eaome/watertanksensor/IMG_5381.jpeg

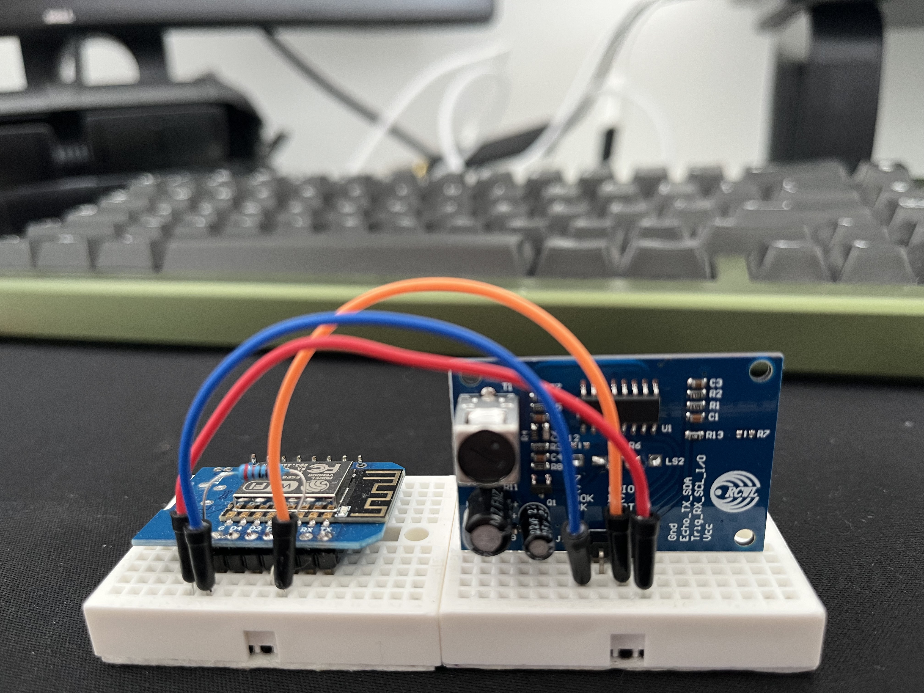
IMG_5381.jpeg
