eaome/watertanksensor/IMG_5385.jpeg

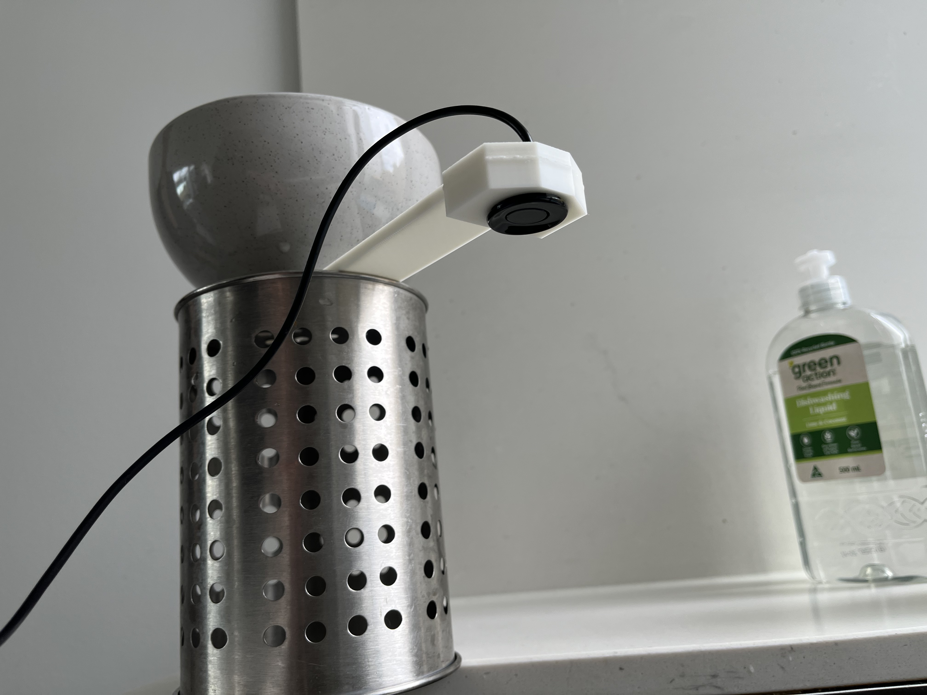
IMG_5385.jpeg
