eaome/watertanksensor/IMG_5386 2.PNG

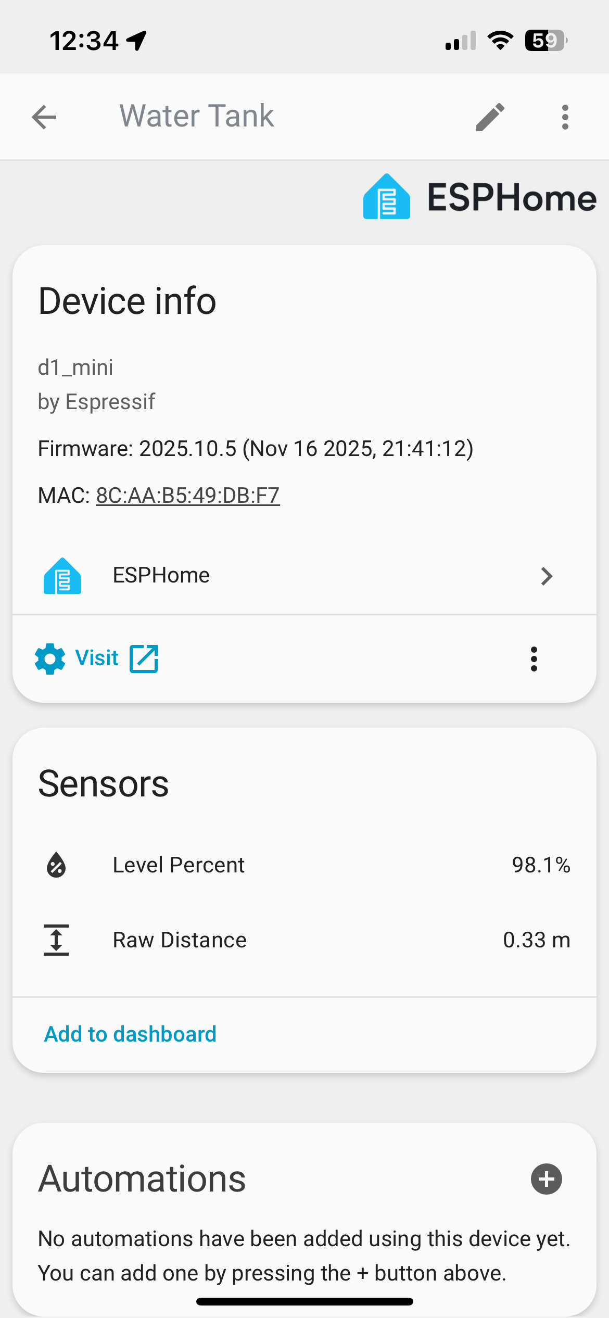
IMG_5386 2.PNG
