eaome/watertanksensor/IMG_5388.jpeg

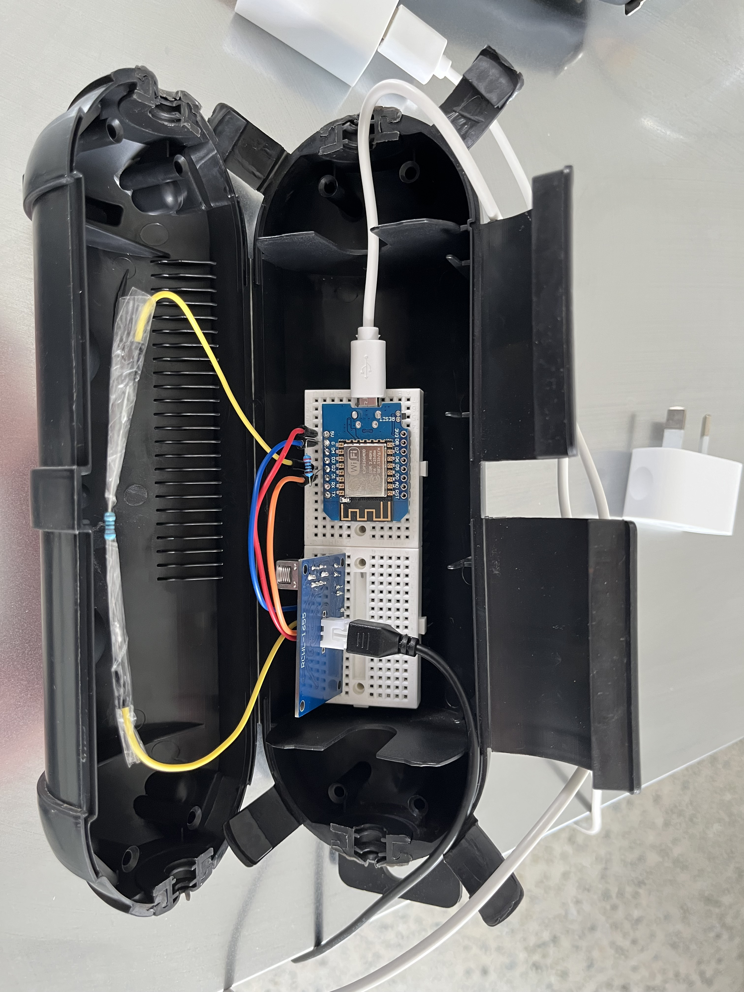
IMG_5388.jpeg
