eaome/watertanksensor/IMG_5384.jpeg

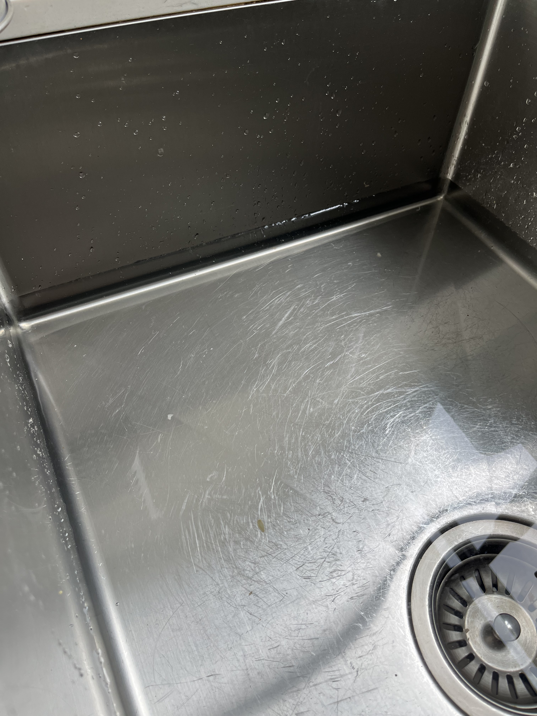
IMG_5384.jpeg
