eaome/watertanksensor/IMG_5390.jpeg

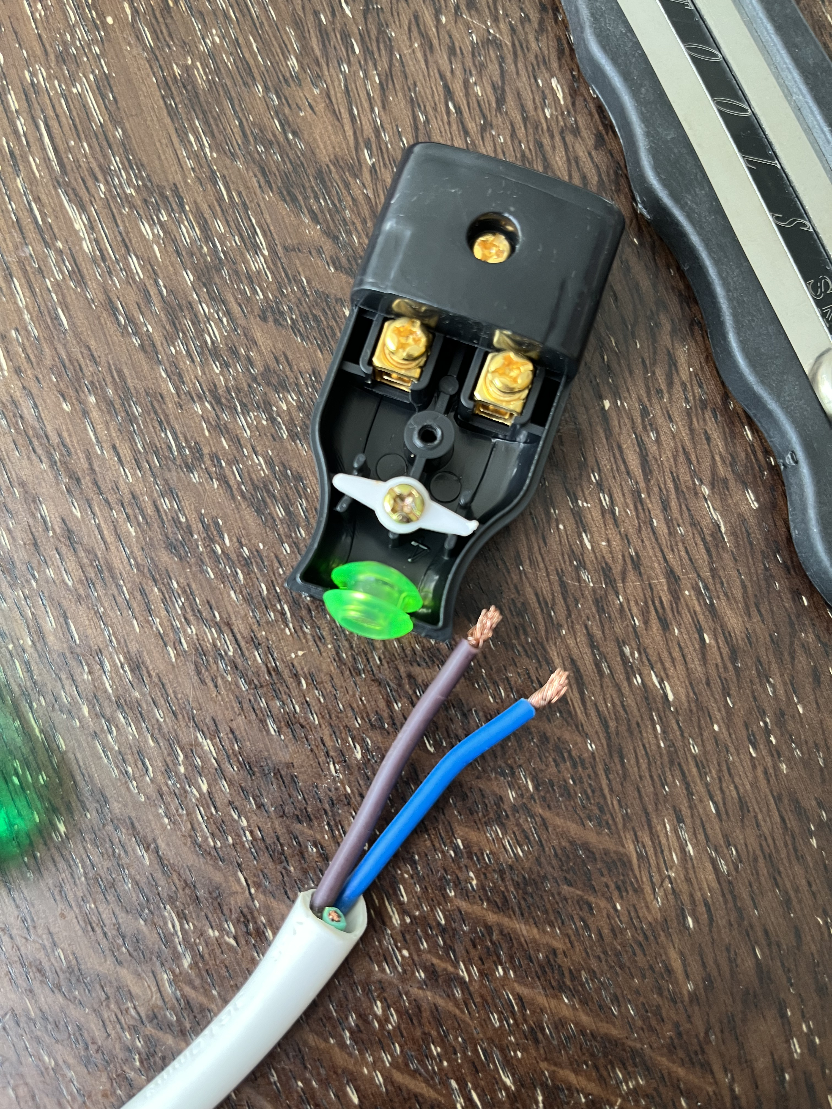
IMG_5390.jpeg
