eaome/watertanksensor/IMG_5391.jpeg

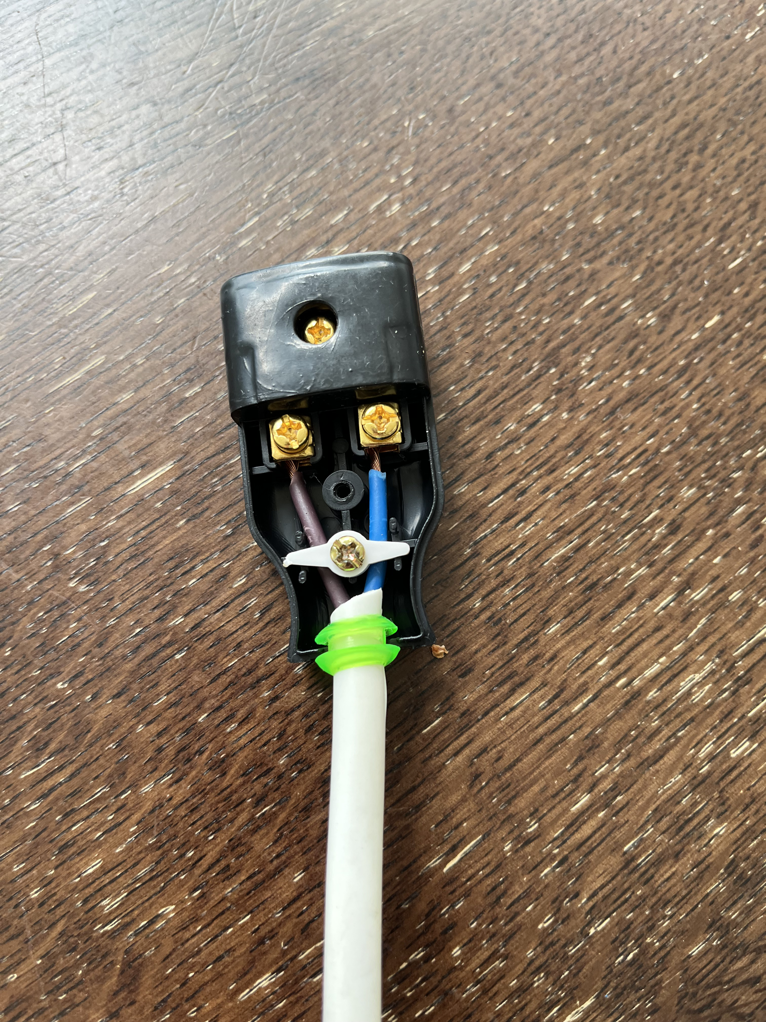
IMG_5391.jpeg
