eaome/watertanksensor/IMG_5393.jpeg

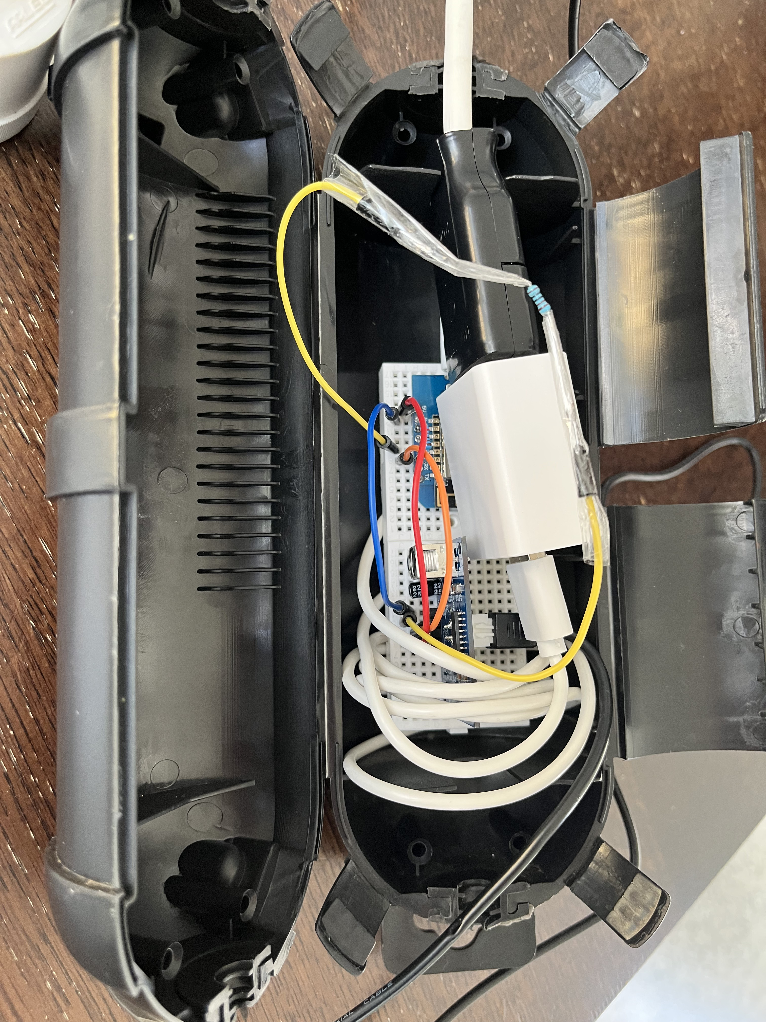
IMG_5393.jpeg
